atopile/swoop/elec/src/usb-connectors/README.md

# USB Connectors

## Installation
Run in the terminal:

```ato install usb-connectors```

Add to your `.ato` project:

```import USBCConn from "usb-connectors/usb-connectors.ato"```

## Overview

This package includes a usb-c connector.

![usbc](https://assets.lcsc.com/images/lcsc/900x900/20230202_Shenzhen-Kinghelm-Elec-KH-TYPE-C-16P_C709357_front.jpg)

## Features

- **USB type C connector**
- **Two cc resistors:** Those set the charge current to three amps.

## Documentation & Resources

- [A bit more about the CC resistors](https://hackaday.com/2023/01/04/all-about-usb-c-resistors-and-emarkers/)
- [LCSC part number](https://www.lcsc.com/product-detail/USB-Connectors_Shenzhen-Kinghelm-Elec-KH-TYPE-C-16P_C709357.html)

## Contributing

Contribute to this package using pull requests.

## License

This usb module is provided under the [MIT License](https://opensource.org/license/mit/).

## Contact

For further inquiries or support, please contact me at [narayan@atopile.io](mailto:email@example.com).
