atopile/swoop/elec/src/bq24045dsqr/elec/layout/default/bq24045dsqr.kicad_pcb

## KiCad design elec/src/bq24045dsqr/elec/layout/default/bq24045dsqr.kicad_pcb (2024-04-17)

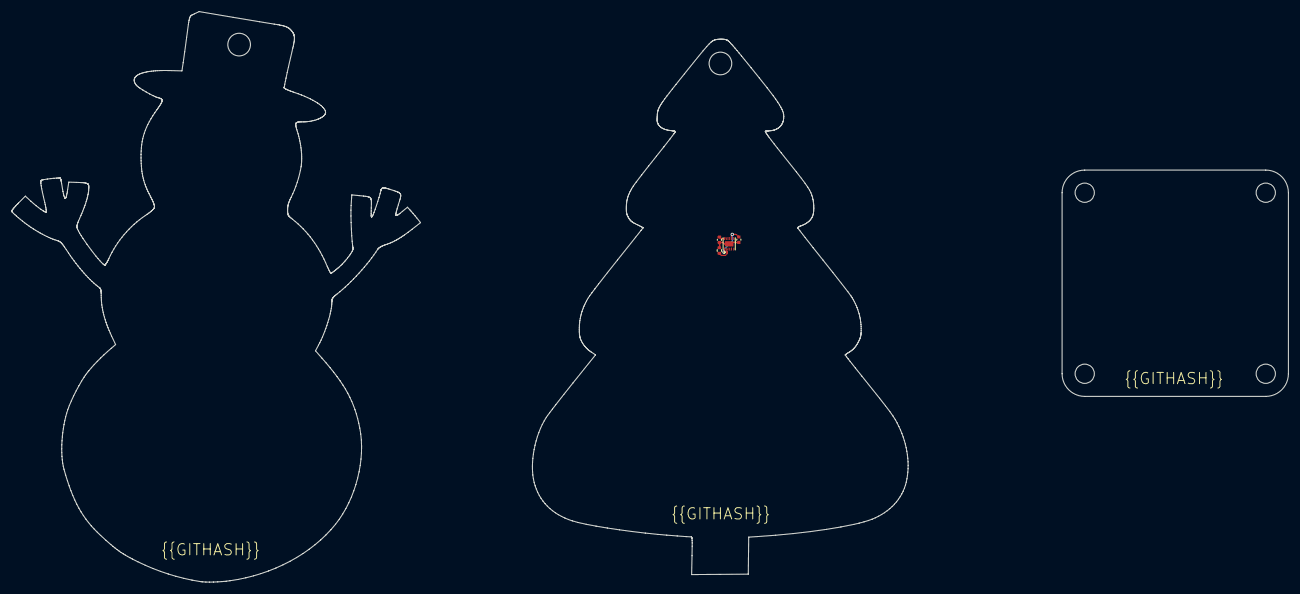
[picture p22: board bq24045dsqr.kicad_pcb from above]

Board: 2 copper layers, 66.4 x 94.6 mm, 4 parts (0 on the bottom side), 4 nets.

Parts:
C1, C2: 25V 1uF X5R ±10% 0402 Multilayer Ceramic Capacito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; C0402
R1: 100mW Thick Film Resistors ±100ppm/℃ ±1% 604Ω 040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; R0402
U1: WSON-10_L2.0-W2.0-P0.40-BL-EP

Connections:
ic-gnd: C1.2, C2.2, R1.2, U1.3, U1.11
ic-vcc: C1.1, U1.1, U1.7
ic-vcc-1: C2.1, U1.10
iset: R1.1, U1.2
