atopile/swoop/elec/src/esp32-s3/elec/layout/default/esp32-s3.kicad_pcb

## KiCad design elec/src/esp32-s3/elec/layout/default/esp32-s3.kicad_pcb (2024-04-17)

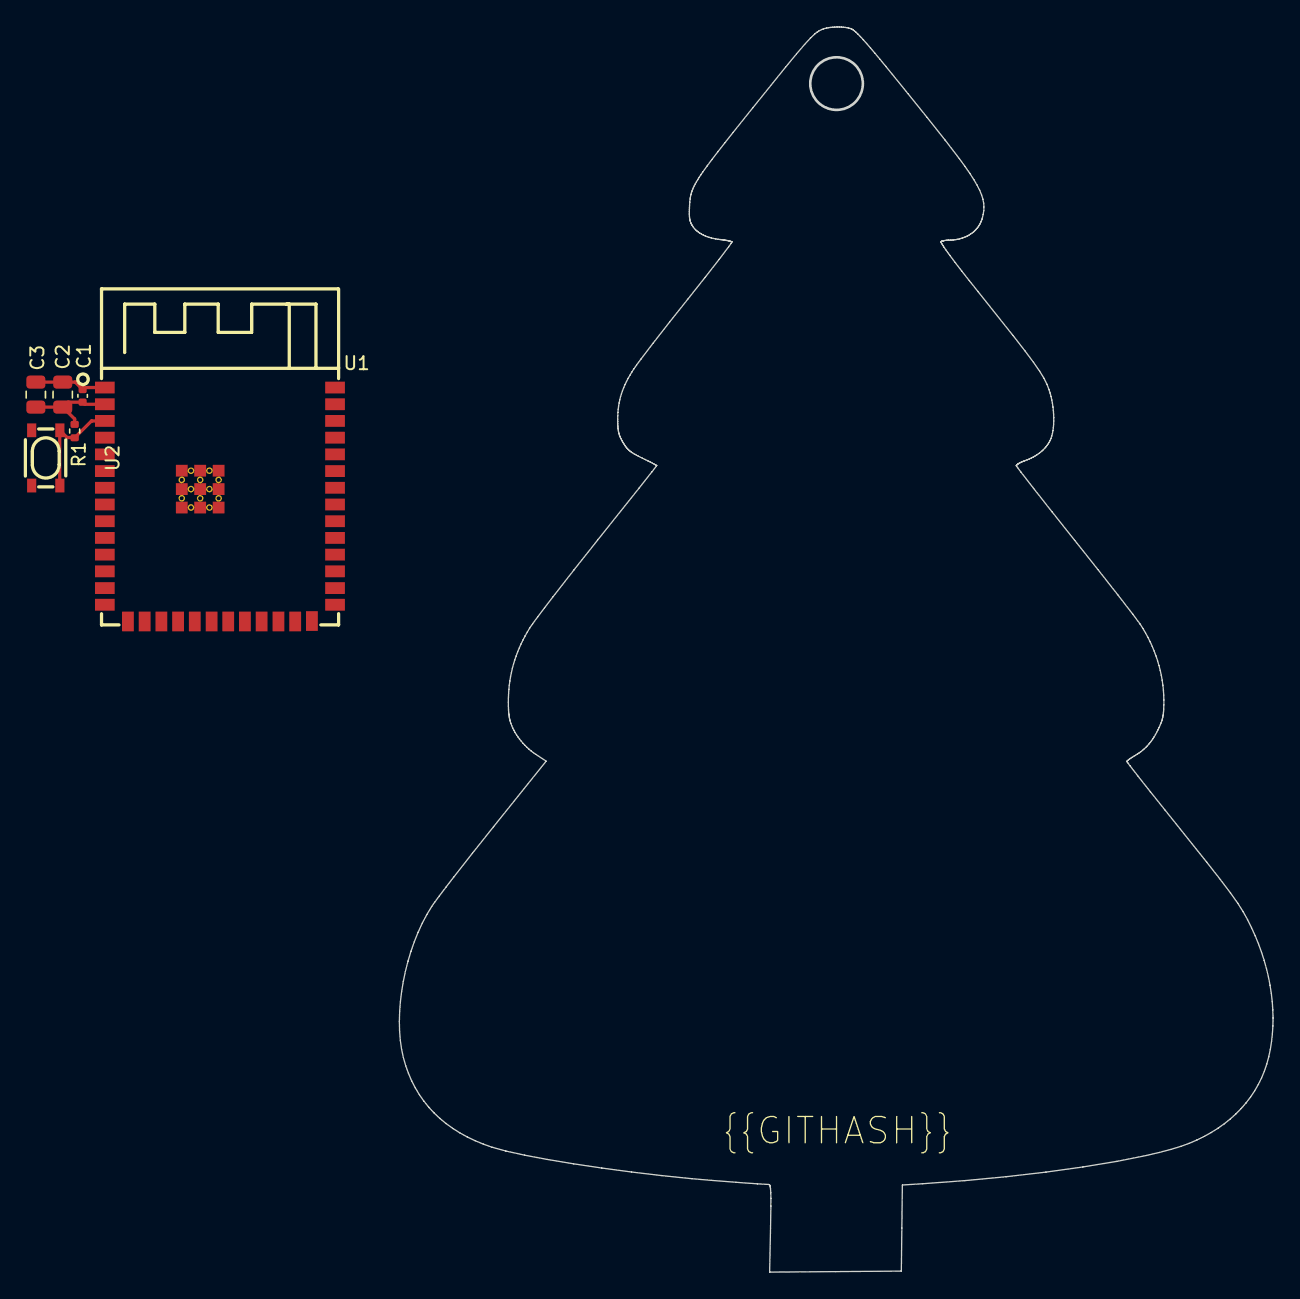
[picture p23: board esp32-s3.kicad_pcb from above]

Board: 2 copper layers, 66.4 x 94.6 mm, 6 parts (0 on the bottom side), 3 nets.

Parts:
C1: 16V 100nF X7R ±10% 0402 Multilayer Ceramic Capaci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; C0402
C2, C3: 25V 10uF X5R ±10% 0805 Multilayer Ceramic Capacit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; C0805
R1: 62.5mW Thick Film Resistors ±100ppm/℃ ±1% 10kΩ 04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; R0402
U1: WIRELM-SMD_ESP32-S3-WROOM-1
U2: KEY-SMD_4P-L4.2-W3.2-P2.20-LS4.6

Connections:
en: R1.2, U1.3, U2.1, U2.2
ic-gnd: C1.2, C2.2, C3.2, U1.1, U1.40, U1.41, U2.3, U2.4
vcc: C1.1, C2.1, C3.1, R1.1, U1.2
