atopile/swoop/elec/src/ams1117-33/elec/layout/default/ams1117-33.kicad_pcb

## KiCad design elec/src/ams1117-33/elec/layout/default/ams1117-33.kicad_pcb (2024-04-17)

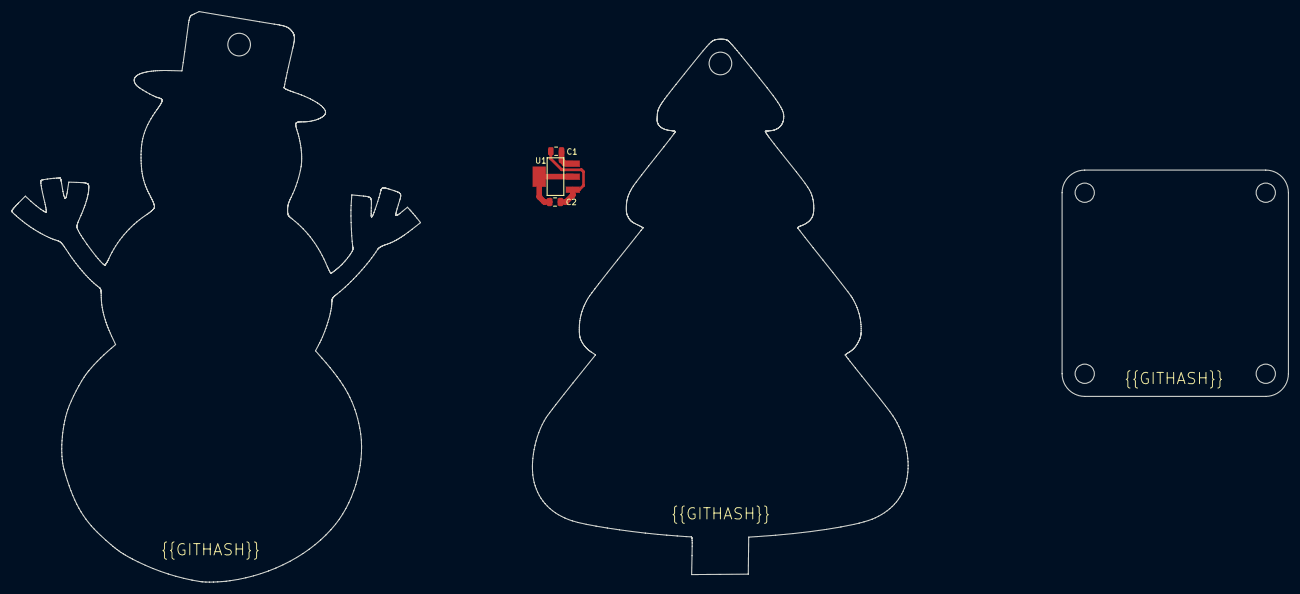
[picture p24: board ams1117-33.kicad_pcb from above]

Board: 2 copper layers, 66.4 x 94.6 mm, 3 parts (0 on the bottom side), 3 nets.

Parts:
C1, C2: 25V 10uF X5R ±10% 0805 Multilayer Ceramic Capacit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; C0805
U1: SOT-223-3_L6.5-W3.4-P2.30-LS7.0-BR

Connections:
gnd: C1.2, C2.2, U1.1
vcc: C1.1, U1.3
vcc-1: C2.1, U1.2, U1.4
