atopile/swoop/elec/src/usb-connectors/elec/layout/default/usbc.kicad_pcb

## KiCad design elec/src/usb-connectors/elec/layout/default/usbc.kicad_pcb (2024-04-17)

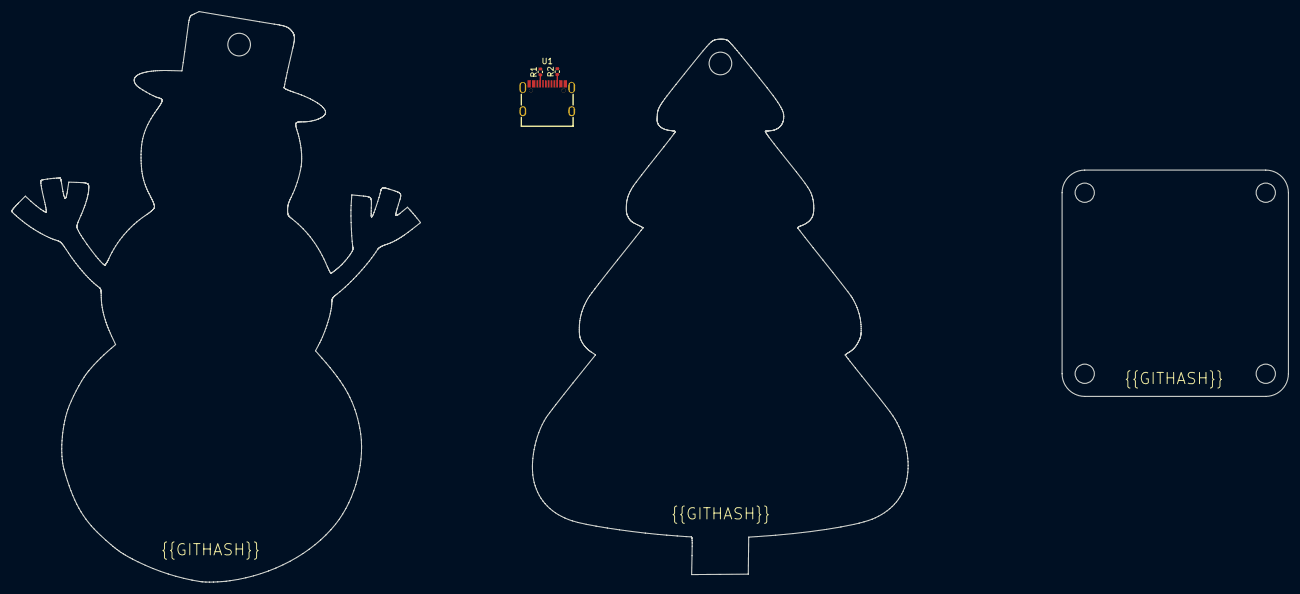
[picture p25: board usbc.kicad_pcb from above]

Board: 2 copper layers, 66.4 x 94.6 mm, 3 parts (0 on the bottom side), 6 nets.

Parts:
R1, R2: Chip Resistor - Surface Mount 4.7KOhms ±5% 1/16W 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; R0402
U1: USB-C-SMD_KH-TYPE-C-16P

Connections:
cc1: R1.1, U1.A5
cc2: R2.1, U1.B5
dm: U1.A7, U1.B7
dp: U1.A6, U1.B6
gnd: R1.2, R2.2, U1.1, U1.2, U1.3, U1.4, U1.A1, U1.A12, U1.B1, U1.B12
vcc: U1.A4, U1.A9, U1.B4, U1.B9
