atopile/swoop/elec/src/tps63020dsjr/elec/layout/default/tps63020dsjr.kicad_pcb

## KiCad design elec/src/tps63020dsjr/elec/layout/default/tps63020dsjr.kicad_pcb (2024-04-17)

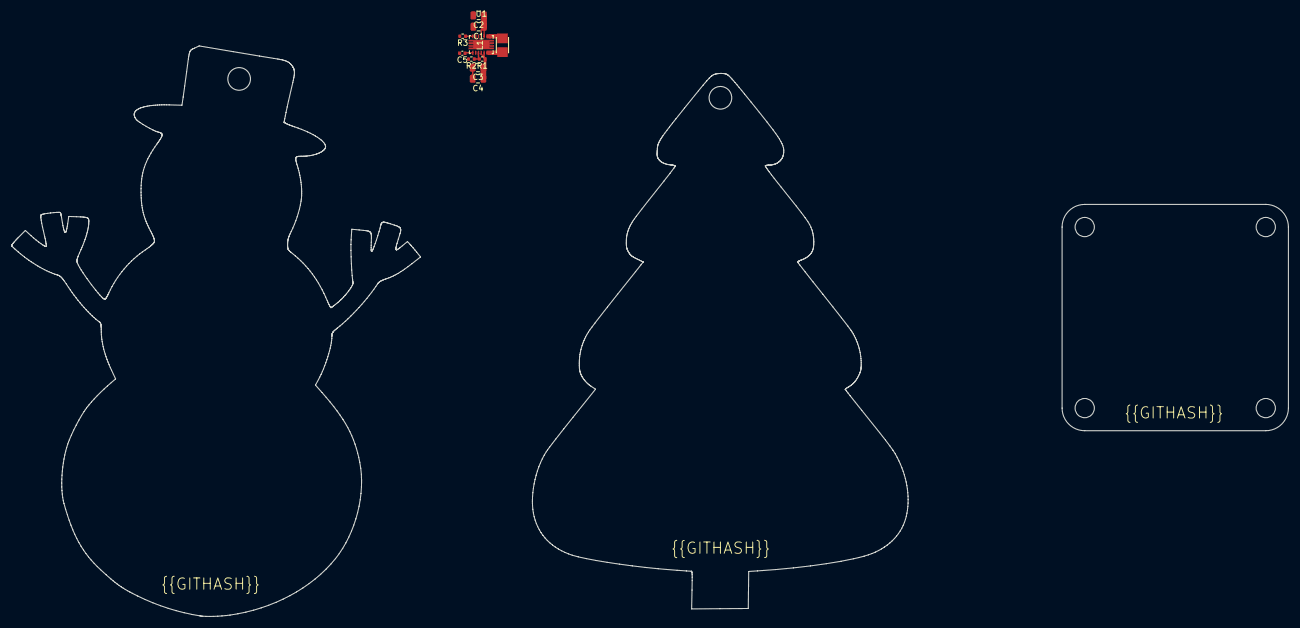
[picture p26: board tps63020dsjr.kicad_pcb from above]

Board: 2 copper layers, 10 parts (0 on the bottom side), 8 nets.

Parts:
C1, C2, C3, C4: Multilayer Ceramic Capacitors MLCC - SMD/SMT 10uF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; C0805
C5: Multilayer Ceramic Capacitors MLCC - SMD/SMT 100n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; C0402
L1: IND-SMD_L2.5-W2.0_WPN252012H
R1, R3: Chip Resistor - Surface Mount 1MOhms ±5% 1/16W 04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; R0402
R2: Chip Resistor - Surface Mount 180KOhms ±5% 1/16W 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; R0402
U1: VSON-14_L4.0-W3.0-P0.50-BL-EP_TI_DSJ

Connections:
gnd: C1.2, C2.2, C3.2, C4.2, C5.2, R2.2, R3.2, U1.2, U1.13, U1.15
l1: L1.1, U1.8, U1.9
l2: L1.2, U1.6, U1.7
out: R1.2, R2.1, U1.3
pg: R3.1, U1.14
vcc: C1.1, C2.1, U1.10, U1.11
vcc-1: C3.1, C4.1, R1.1, U1.4, U1.5
vina: C5.1, U1.1, U1.12
