atopile/swoop/elec/src/ah3772-sa-7/elec/layout/default/ah3772-sa-7.kicad_pcb

## KiCad design elec/src/ah3772-sa-7/elec/layout/default/ah3772-sa-7.kicad_pcb (2024-04-17)

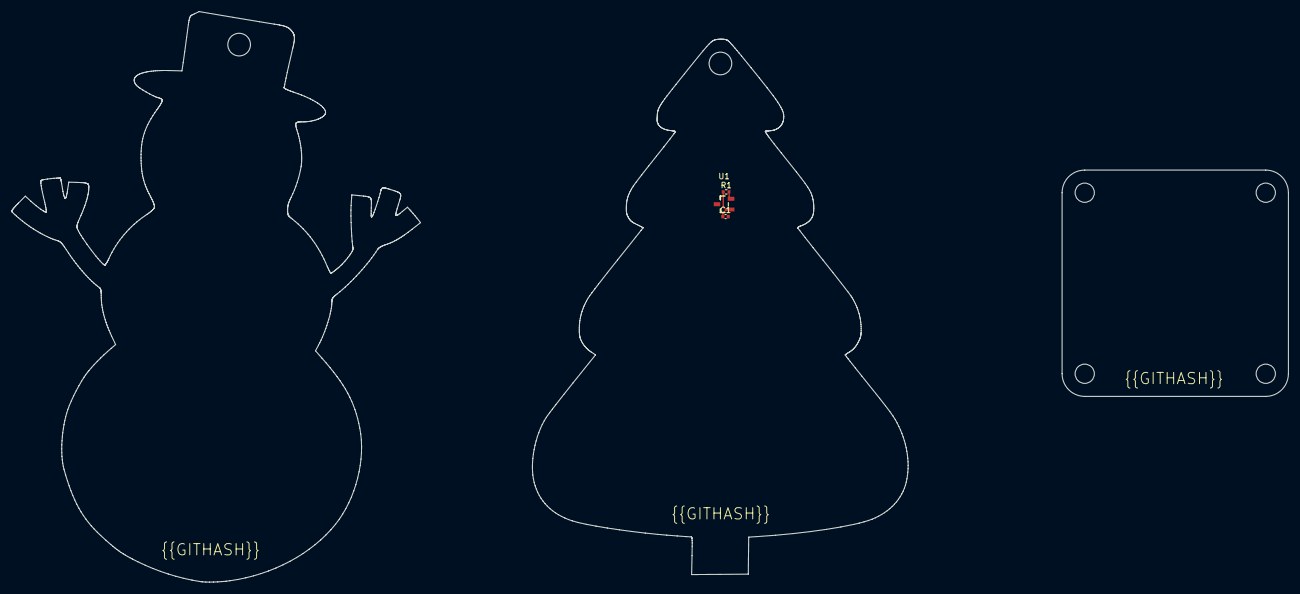
[picture p27: board ah3772-sa-7.kicad_pcb from above]

Board: 2 copper layers, 66.4 x 94.6 mm, 3 parts (0 on the bottom side), 3 nets.

Parts:
C1: 16V 100nF X7R ±10% 0402 Multilayer Ceramic Capaci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; C0402
R1: Chip Resistor - Surface Mount 1KOhms ±5% 1/16W 04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; R0402
U1: SOT-23-3_L2.9-W1.3-P1.90-LS2.4-BR-CW

Connections:
gnd: C1.2, U1.2
out: R1.2, U1.3
vcc: C1.1, R1.1, U1.1
